blurpy/8-bit-computer/resources/8-bit-computer-fritzing.png

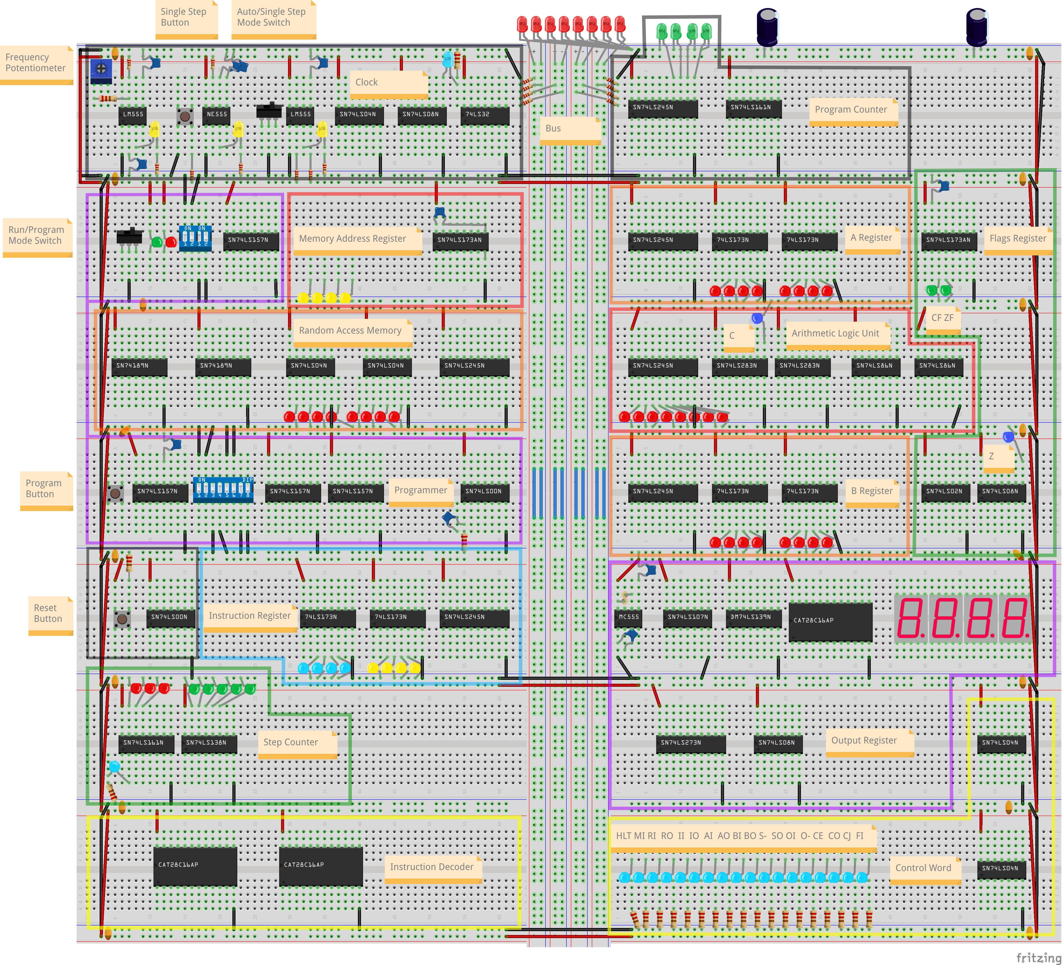
resources/8-bit-computer-fritzing.png
